HUANGJIN169/CAE32/Mecanismos/Archivos_STL/Modulo_AS5600_p/1.png

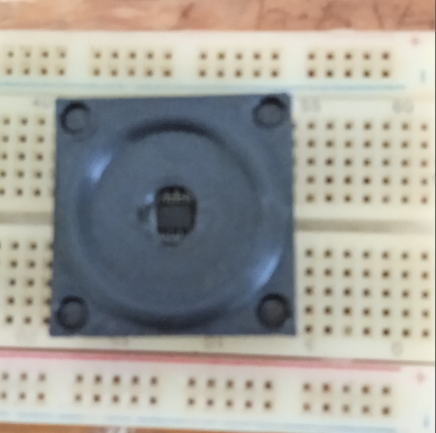
Mecanismos/Archivos_STL/Modulo_AS5600_p/1.png
