HUANGJIN169/CAE32/Mecanismos/Archivos_STL/D#2/EJE_reatroalimentacion-Body.3mf.amf

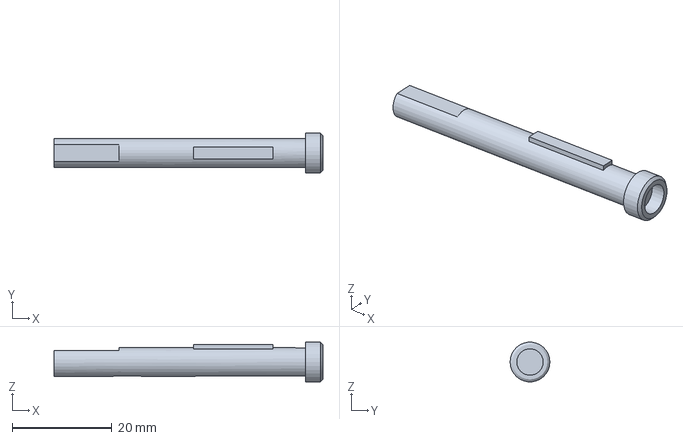
[picture p27: CAD file, 2023-01-21]
Mecanismos/Archivos_STL/D#2/EJE_reatroalimentacion-Body.3mf.amf
54.0 x 8.00 x 7.96 mm
