HUANGJIN169/CAE32/Mecanismos/Archivos_STL/Modulo_AS5600_p/Struct_1.stl

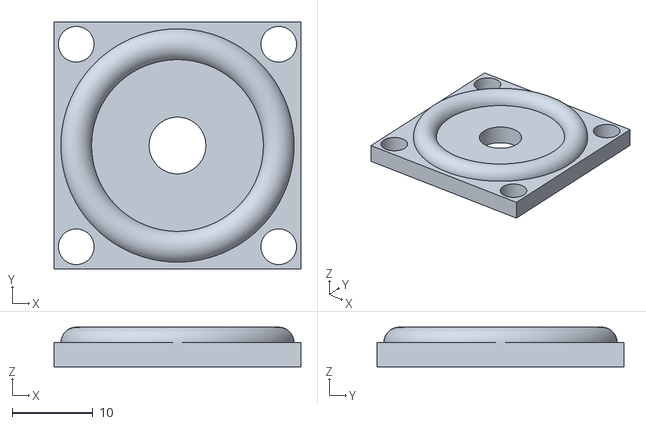
[picture p28: CAD file, 2022-06-30]
Mecanismos/Archivos_STL/Modulo_AS5600_p/Struct_1.stl
30.5 x 30.5 x 4.90
