HUANGJIN169/CAE32/Mecanismos/Shifter/amf/soporte-Body.amf

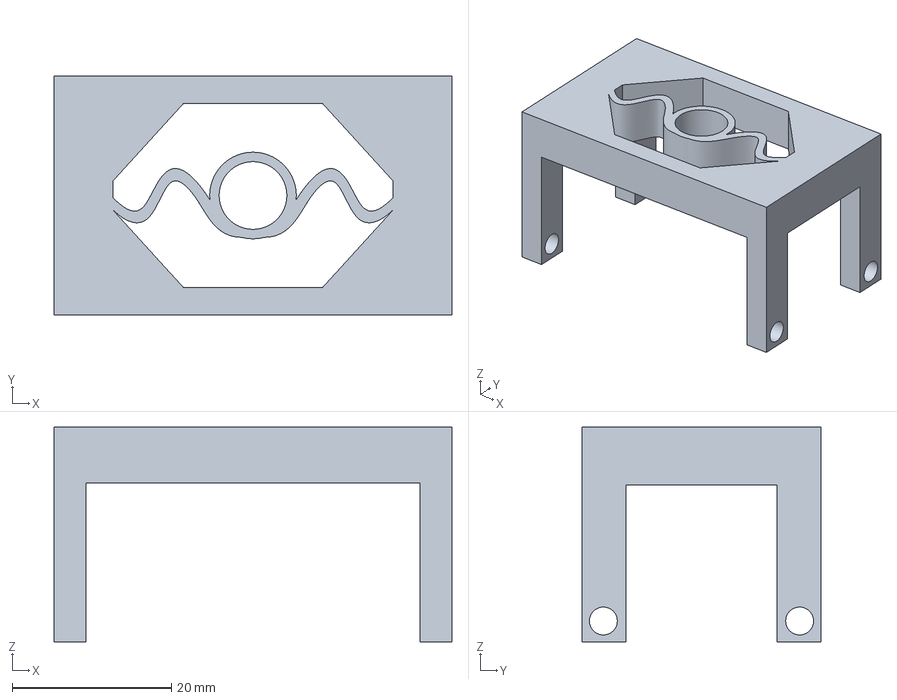
[picture p29: CAD file, 2023-01-31]
Mecanismos/Shifter/amf/soporte-Body.amf
50.0 x 30.0 x 27.0 mm
