HUANGJIN169/CAE32/Mecanismos/Shifter/Tapa.FCStd

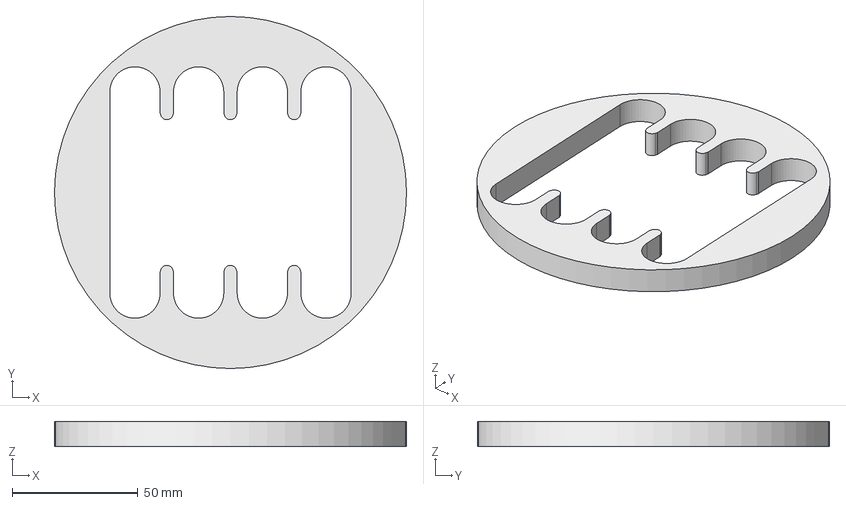
[picture p30: CAD file, 2023-01-31]
Mecanismos/Shifter/Tapa.FCStd
140.0 x 140.0 x 10.0 mm
