HUANGJIN169/CAE32/Mecanismos/Archivos_freecad/Banco_de_pruebas_AS5600/Ensamble_modulo_as5600/Base_iman_bal.FCStd

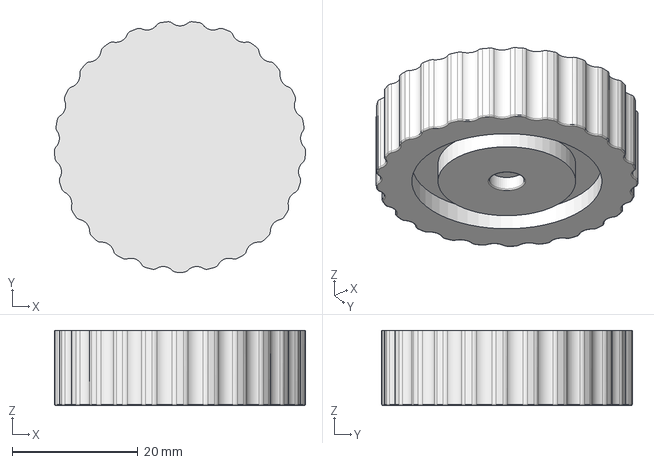
[picture p31: CAD file, 2022-06-30]
Mecanismos/Archivos_freecad/Banco_de_pruebas_AS5600/Ensamble_modulo_as5600/Base_iman_bal.FCStd
40.0 x 39.9 x 12.0 mm
