HUANGJIN169/CAE32/Mecanismos/Archivos_freecad/Case_para_pilas/portapilas.FCStd

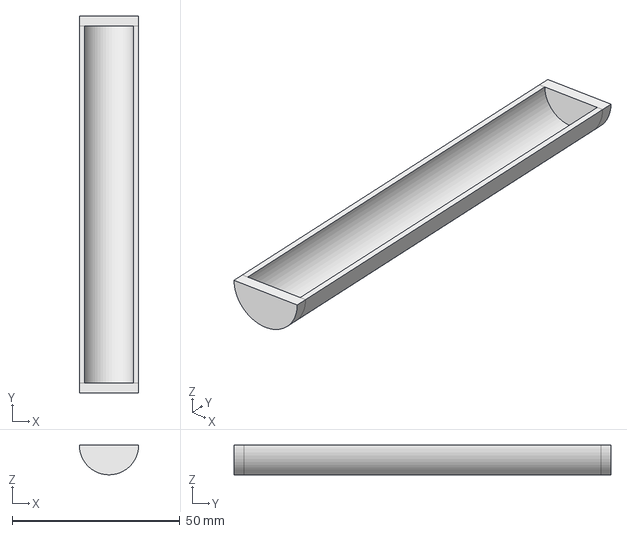
[picture p32: CAD file, 2022-09-12]
Mecanismos/Archivos_freecad/Case_para_pilas/portapilas.FCStd
17.7 x 112.5 x 8.85 mm
