HUANGJIN169/CAE32/Mecanismos/Archivos_freecad/D#2/espaciador.FCStd

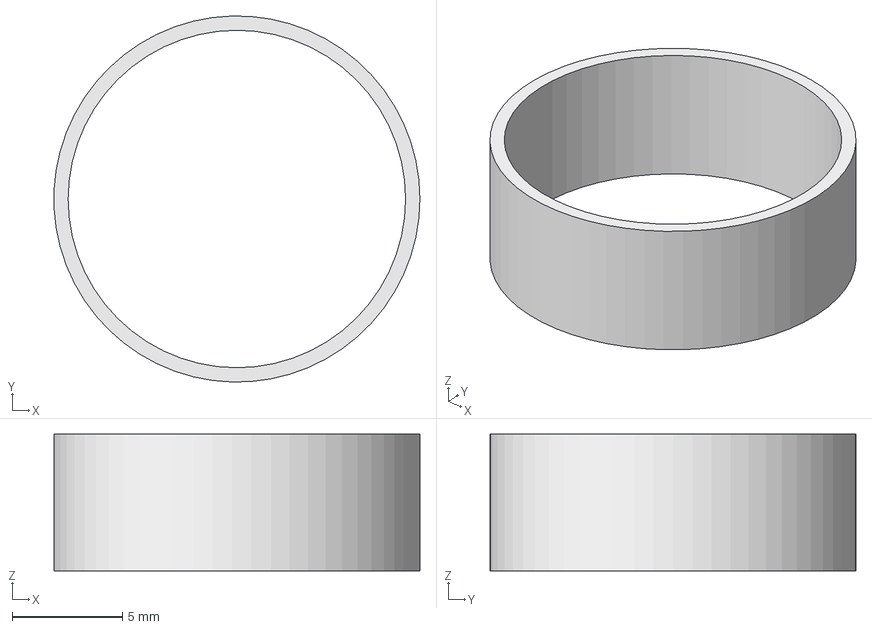
[picture p33: CAD file, 2023-01-21]
Mecanismos/Archivos_freecad/D#2/espaciador.FCStd
16.6 x 16.6 x 6.20 mm
