HUANGJIN169/CAE32/Mecanismos/Archivos_freecad/Simulación_de_pedales/Modelo_1/stl/medidor-Body.stl

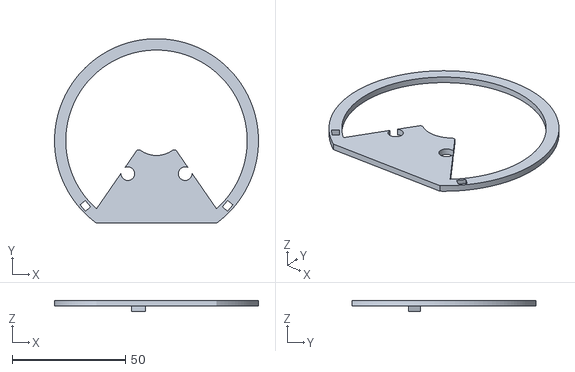
[picture p34: CAD file, 2022-09-18]
Mecanismos/Archivos_freecad/Simulación_de_pedales/Modelo_1/stl/medidor-Body.stl
90.0 x 81.4 x 5.00
