HUANGJIN169/CAE32/Mecanismos/Archivos_freecad/Simulación_de_pedales/Modelo_2/engrane.FCStd

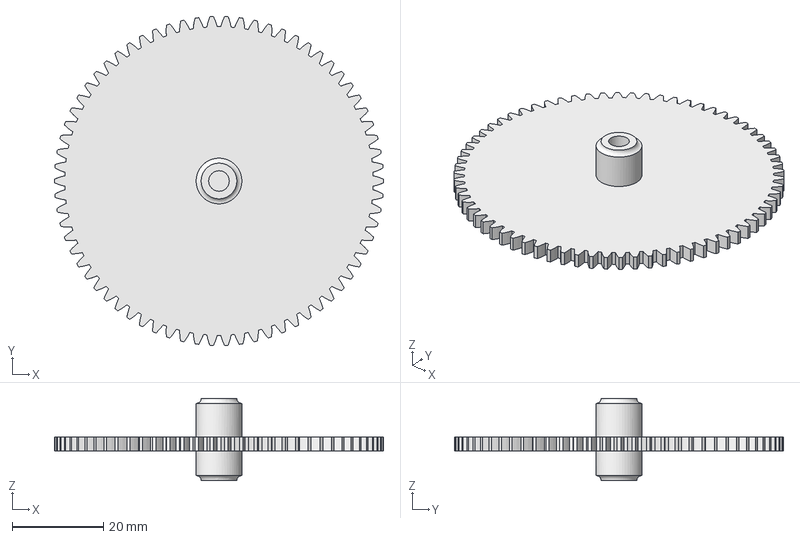
[picture p35: CAD file, 2022-09-12]
Mecanismos/Archivos_freecad/Simulación_de_pedales/Modelo_2/engrane.FCStd
72.0 x 72.0 x 18.0 mm
