HUANGJIN169/CAE32/Mecanismos/Archivos_freecad/Simulación_de_pedales/Modelo_3/Engrane_motor_V2.FCStd

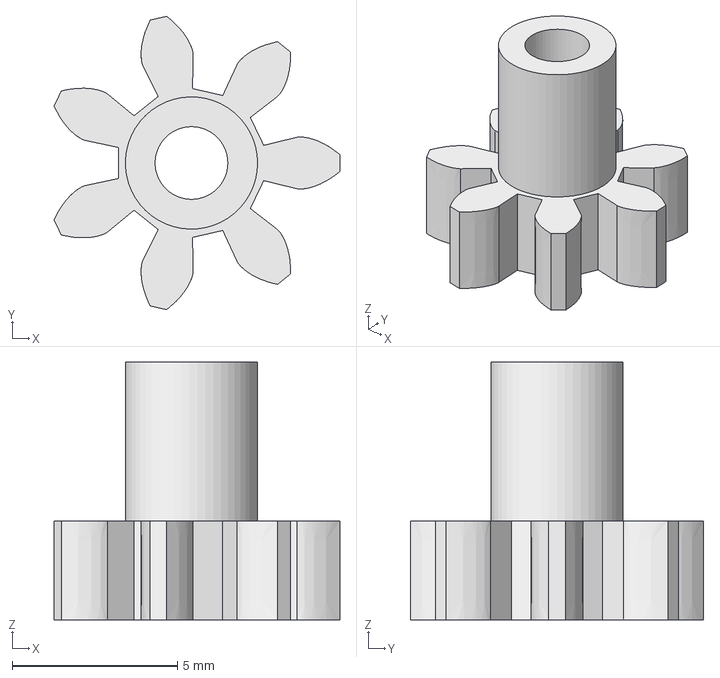
[picture p36: CAD file, 2022-09-15]
Mecanismos/Archivos_freecad/Simulación_de_pedales/Modelo_3/Engrane_motor_V2.FCStd
8.65 x 8.87 x 7.80 mm
