HUANGJIN169/CAE32/Mecanismos/Archivos_freecad/Simulación_de_pedales/Modelo_4/display.FCStd

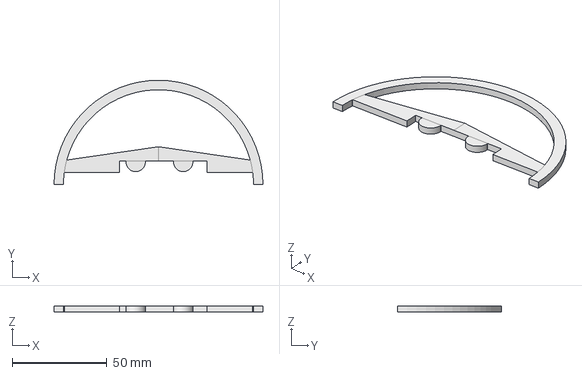
[picture p37: CAD file, 2022-09-12]
Mecanismos/Archivos_freecad/Simulación_de_pedales/Modelo_4/display.FCStd
110.0 x 55.0 x 3.00 mm
