HUANGJIN169/CAE32/Mecanismos/Archivos_freecad/Sistema_mecanico_pedales/Pedales/freno_embrague.FCStd

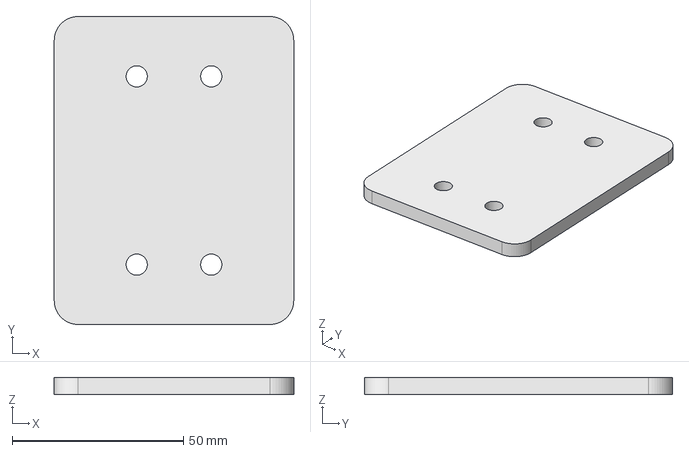
[picture p38: CAD file, 2022-07-07]
Mecanismos/Archivos_freecad/Sistema_mecanico_pedales/Pedales/freno_embrague.FCStd
70.0 x 90.0 x 5.00 mm
