HUANGJIN169/CAE32/Mecanismos/Archivos_freecad/Banco_de_pruebas_AS5600/Ensamble_modulo_as5600/Modulo_as5600.FCStd

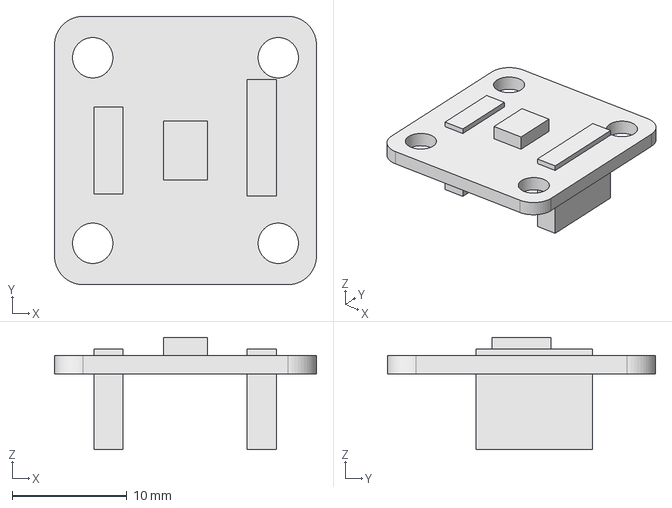
[picture p39: CAD file, 2022-06-30]
Mecanismos/Archivos_freecad/Banco_de_pruebas_AS5600/Ensamble_modulo_as5600/Modulo_as5600.FCStd
22.9 x 23.4 x 9.80 mm
