HUANGJIN169/CAE32/Mecanismos/Archivos_freecad/Simulación_de_pedales/Modelo_1/stl/tope2-Body.stl

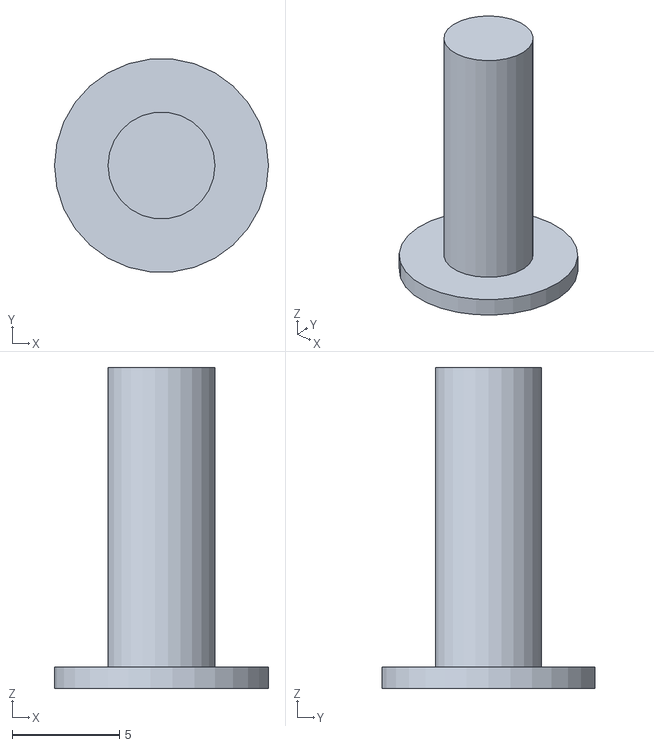
[picture p40: CAD file, 2022-09-18]
Mecanismos/Archivos_freecad/Simulación_de_pedales/Modelo_1/stl/tope2-Body.stl
10.0 x 9.95 x 15.0
