HUANGJIN169/CAE32/Mecanismos/Archivos_freecad/Simulación_de_pedales/Modelo_2/frame.FCStd

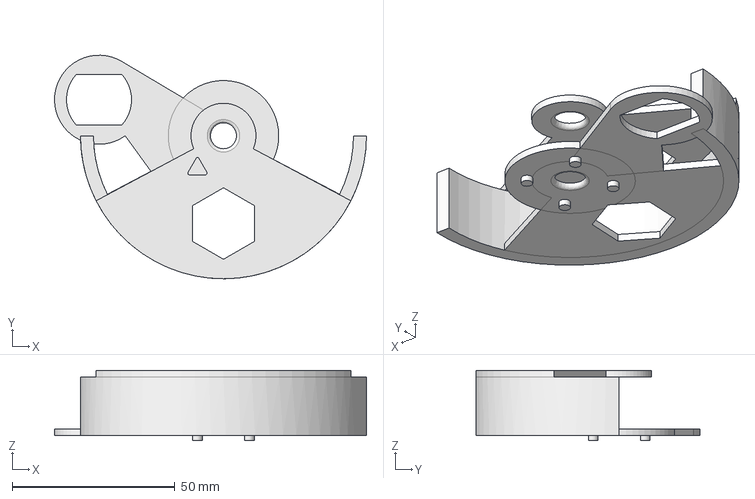
[picture p41: CAD file, 2022-09-12]
Mecanismos/Archivos_freecad/Simulación_de_pedales/Modelo_2/frame.FCStd
96.0 x 68.8 x 21.6 mm
