HUANGJIN169/CAE32/Mecanismos/Archivos_freecad/Simulación_de_pedales/Modelo_3/soporte_marcador2.FCStd

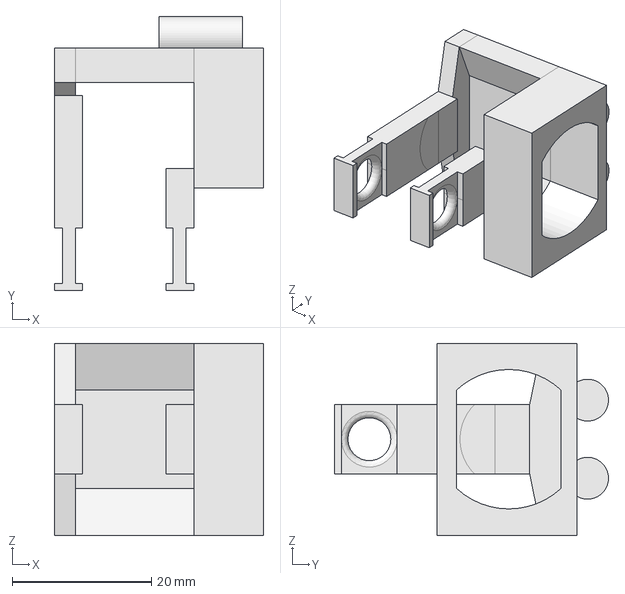
[picture p42: CAD file, 2022-09-12]
Mecanismos/Archivos_freecad/Simulación_de_pedales/Modelo_3/soporte_marcador2.FCStd
30.0 x 39.3 x 27.6 mm
