HUANGJIN169/CAE32/Mecanismos/Archivos_freecad/Simulación_de_pedales/Modelo_4/soporteuno.FCStd

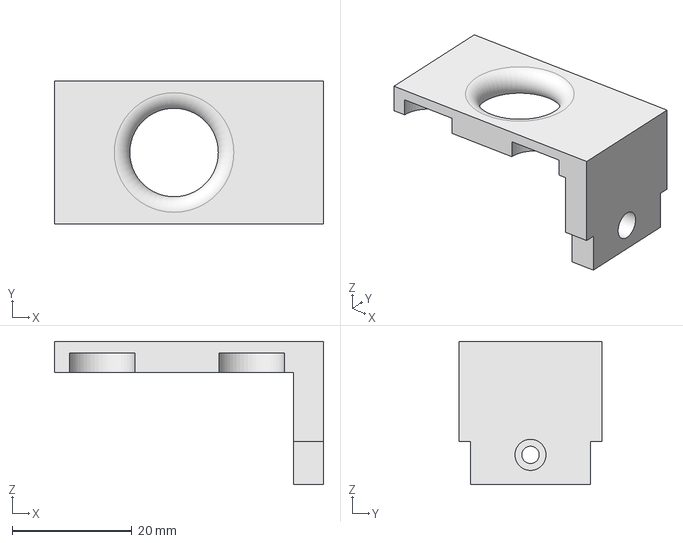
[picture p43: CAD file, 2022-09-12]
Mecanismos/Archivos_freecad/Simulación_de_pedales/Modelo_4/soporteuno.FCStd
45.0 x 24.0 x 24.0 mm
