HUANGJIN169/CAE32/Mecanismos/Archivos_freecad/Simulación_de_pedales/Piezas_frecuentes/medidor.FCStd

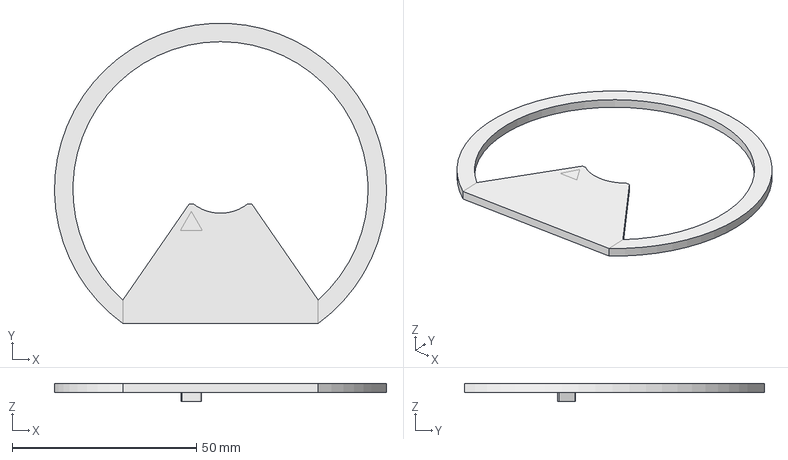
[picture p44: CAD file, 2022-09-12]
Mecanismos/Archivos_freecad/Simulación_de_pedales/Piezas_frecuentes/medidor.FCStd
90.0 x 81.3 x 5.00 mm
