HUANGJIN169/CAE32/Mecanismos/Archivos_STL/D#2/Eje_engrane.amf

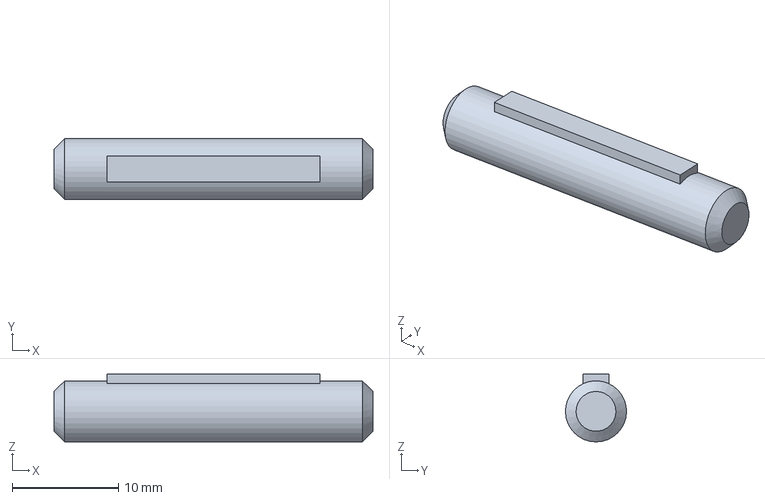
[picture p45: CAD file, 2023-01-21]
Mecanismos/Archivos_STL/D#2/Eje_engrane.amf
30.0 x 5.75 x 6.39 mm
