HUANGJIN169/CAE32/Mecanismos/Archivos_freecad/Simulación_de_pedales/Modelo_3/marcador.FCStd

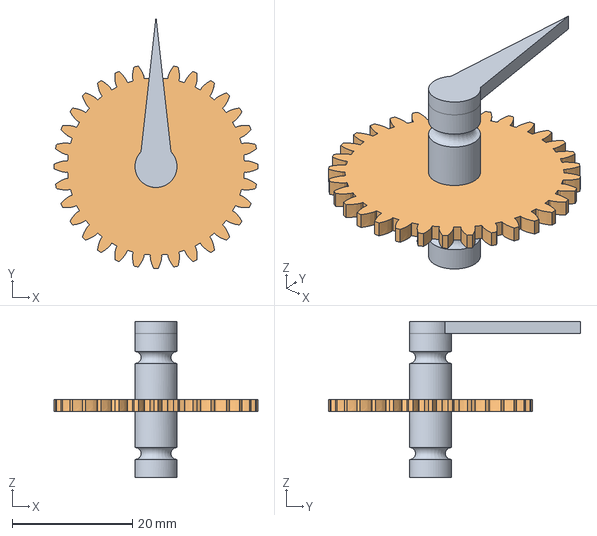
[picture p46: CAD file, 2022-09-12]
Mecanismos/Archivos_freecad/Simulación_de_pedales/Modelo_3/marcador.FCStd
34.0 x 42.0 x 26.0 mm
