HUANGJIN169/CAE32/Mecanismos/Archivos_freecad/Simulación_de_pedales/Modelo_4/Copia de soportedos.FCStd

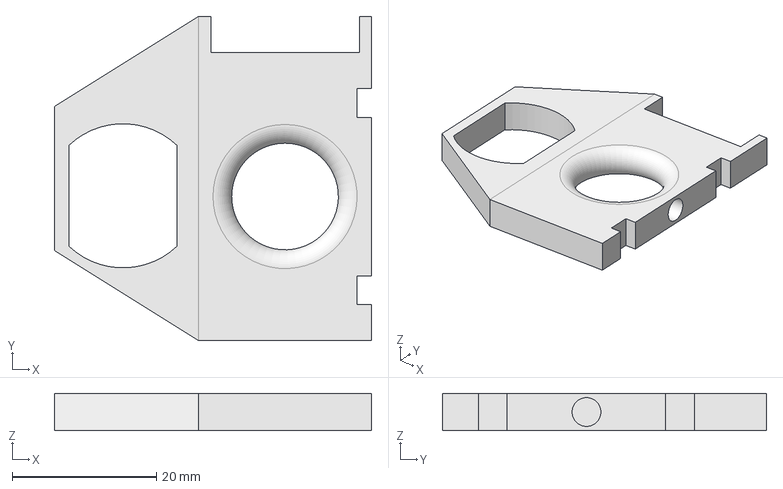
[picture p47: CAD file, 2022-09-12]
Mecanismos/Archivos_freecad/Simulación_de_pedales/Modelo_4/Copia de soportedos.FCStd
44.0 x 45.0 x 5.20 mm
