HUANGJIN169/CAE32/Mecanismos/Archivos_freecad/Simulación_de_pedales/Piezas_frecuentes/motores.FCStd

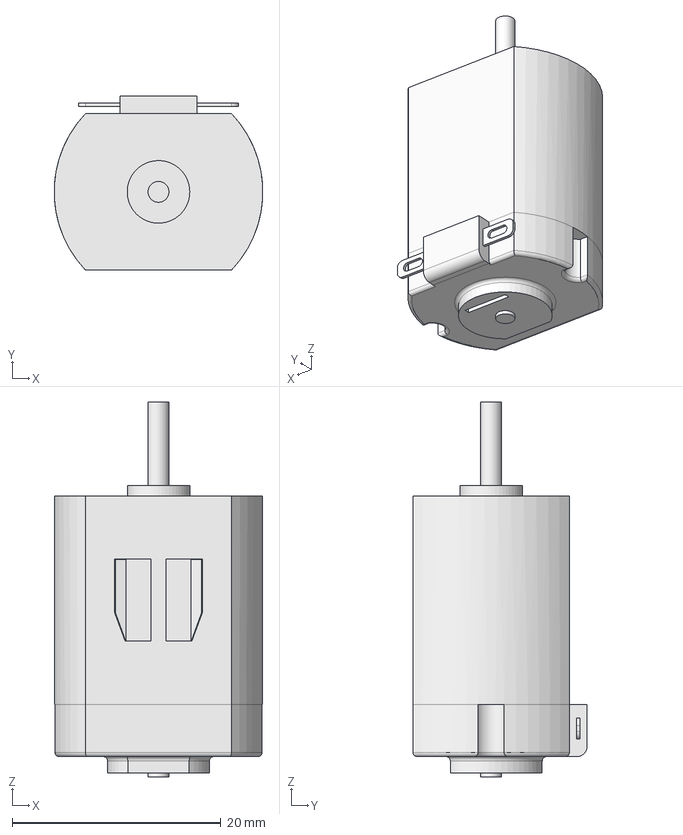
[picture p48: CAD file, 2022-09-12]
Mecanismos/Archivos_freecad/Simulación_de_pedales/Piezas_frecuentes/motores.FCStd
20.0 x 16.7 x 36.0 mm
