HUANGJIN169/CAE32/Mecanismos/Archivos_STL/D#2/Engrane_Parametrico-BodyPocket.amf

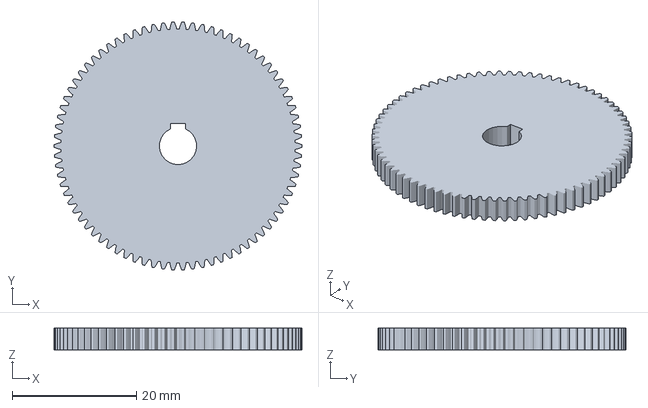
[picture p49: CAD file, 2023-01-21]
Mecanismos/Archivos_STL/D#2/Engrane_Parametrico-BodyPocket.amf
40.0 x 40.0 x 3.50 mm
