HUANGJIN169/CAE32/Mecanismos/Archivos_freecad/Banco_de_pruebas_AS5600/Ensamble_modulo_as5600/iman.FCStd

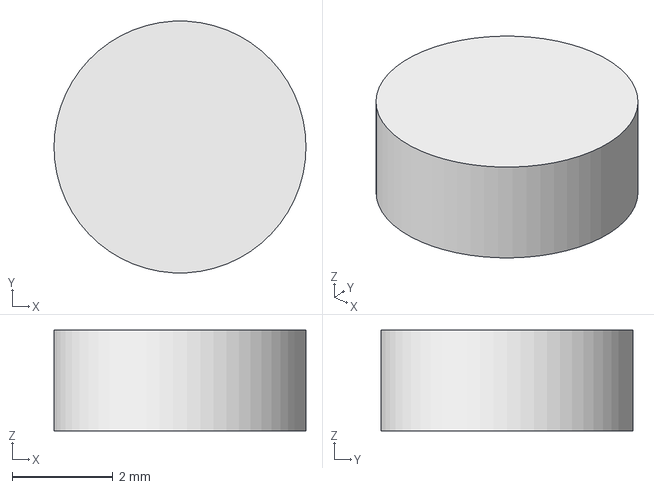
[picture p50: CAD file, 2022-06-30]
Mecanismos/Archivos_freecad/Banco_de_pruebas_AS5600/Ensamble_modulo_as5600/iman.FCStd
5.00 x 4.99 x 2.00 mm
