HUANGJIN169/CAE32/Mecanismos/Archivos_freecad/D#2/case1.FCStd

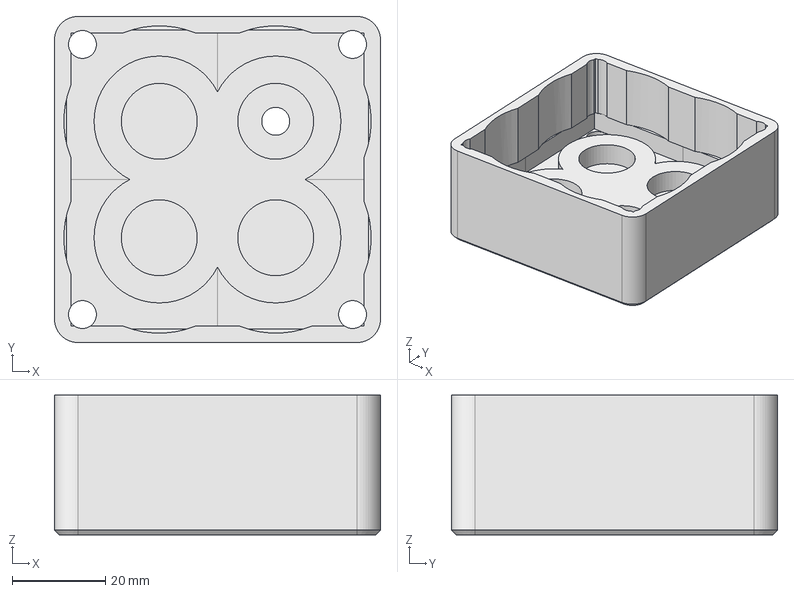
[picture p51: CAD file, 2022-11-13]
Mecanismos/Archivos_freecad/D#2/case1.FCStd
70.0 x 70.0 x 30.0 mm
