HUANGJIN169/CAE32/Mecanismos/Archivos_freecad/Simulación_de_pedales/Modelo_1/imprimir.FCStd

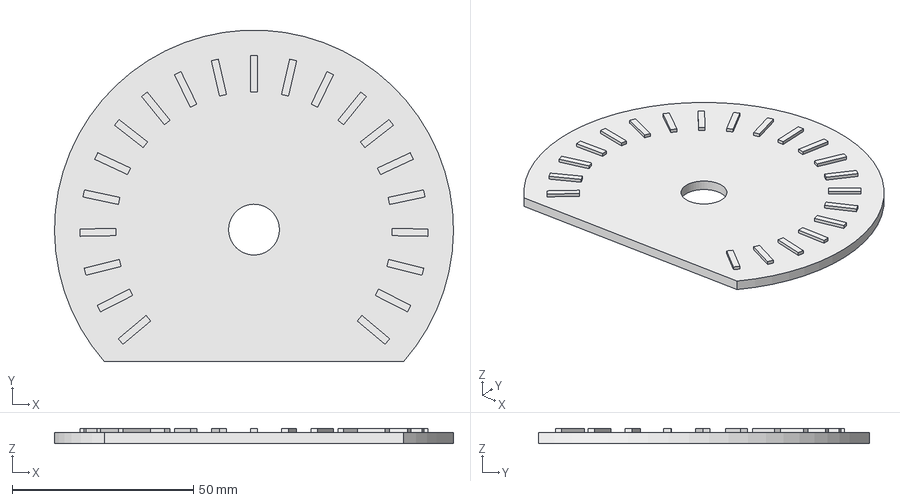
[picture p52: CAD file, 2022-09-18]
Mecanismos/Archivos_freecad/Simulación_de_pedales/Modelo_1/imprimir.FCStd
110.0 x 91.3 x 4.00 mm
