HUANGJIN169/CAE32/Mecanismos/Archivos_freecad/Simulación_de_pedales/Modelo_1/stl/intermedio-Body.stl

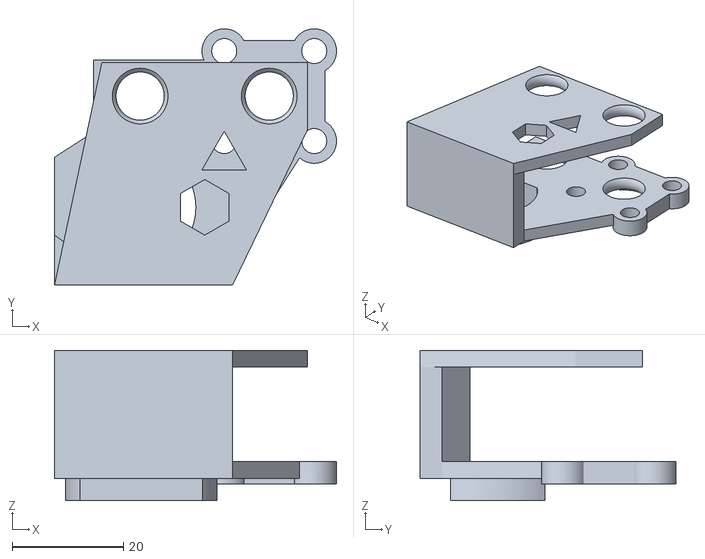
[picture p53: CAD file, 2022-09-16]
Mecanismos/Archivos_freecad/Simulación_de_pedales/Modelo_1/stl/intermedio-Body.stl
50.7 x 46.1 x 27.0
