HUANGJIN169/CAE32/Mecanismos/Archivos_freecad/Simulación_de_pedales/Modelo_4/union_apuntador.FCStd

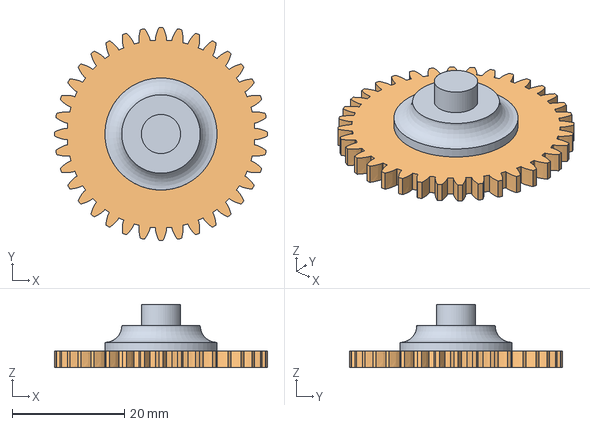
[picture p54: CAD file, 2022-09-12]
Mecanismos/Archivos_freecad/Simulación_de_pedales/Modelo_4/union_apuntador.FCStd
38.0 x 38.0 x 11.3 mm
