HUANGJIN169/CAE32/Mecanismos/Archivos_freecad/D#2/Balero_Parametrico.FCStd

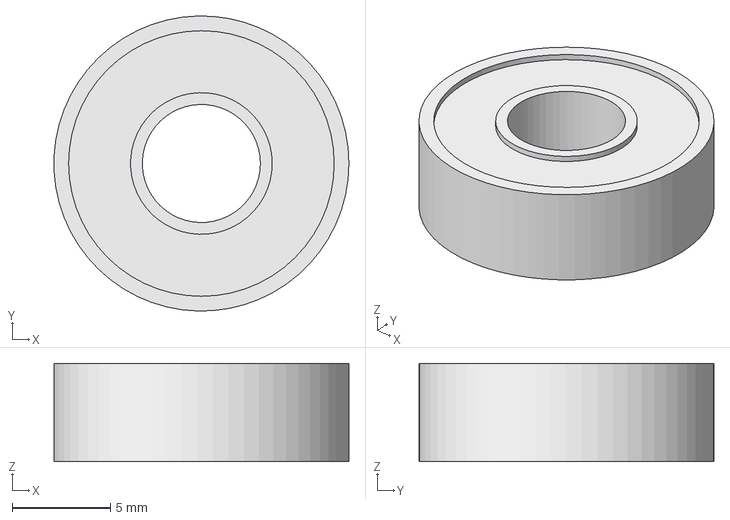
[picture p55: CAD file, 2022-11-08]
Mecanismos/Archivos_freecad/D#2/Balero_Parametrico.FCStd
15.0 x 15.0 x 5.00 mm
