HUANGJIN169/CAE32/Mecanismos/Archivos_freecad/Simulación_de_pedales/Modelo_1/stl/EngraneApuntador-Fusion.stl

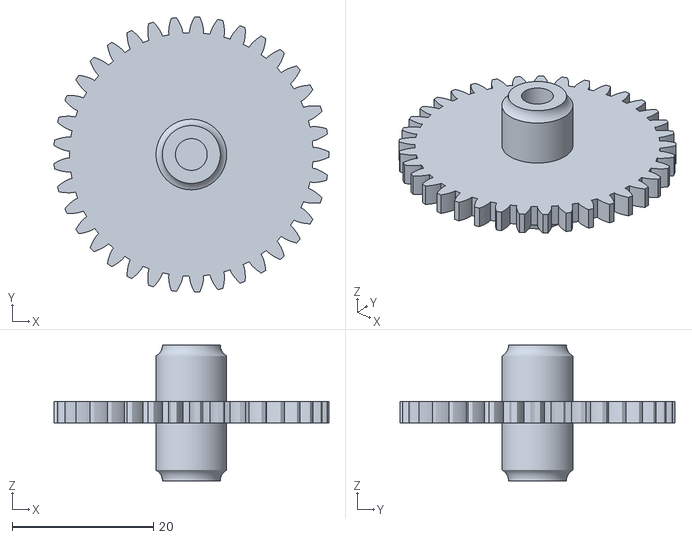
[picture p56: CAD file, 2022-09-16]
Mecanismos/Archivos_freecad/Simulación_de_pedales/Modelo_1/stl/EngraneApuntador-Fusion.stl
39.0 x 39.0 x 19.2
