HUANGJIN169/CAE32/Mecanismos/Archivos_freecad/Simulación_de_pedales/Modelo_1/tope2.FCStd

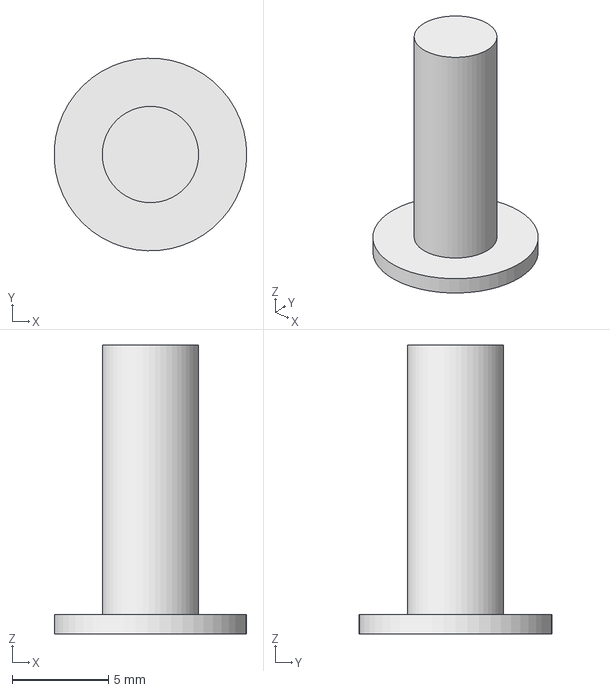
[picture p57: CAD file, 2022-09-18]
Mecanismos/Archivos_freecad/Simulación_de_pedales/Modelo_1/tope2.FCStd
9.99 x 10.00 x 15.0 mm
