HUANGJIN169/CAE32/Mecanismos/Archivos_freecad/Simulación_de_pedales/Modelo_4/engrane_motor.FCStd

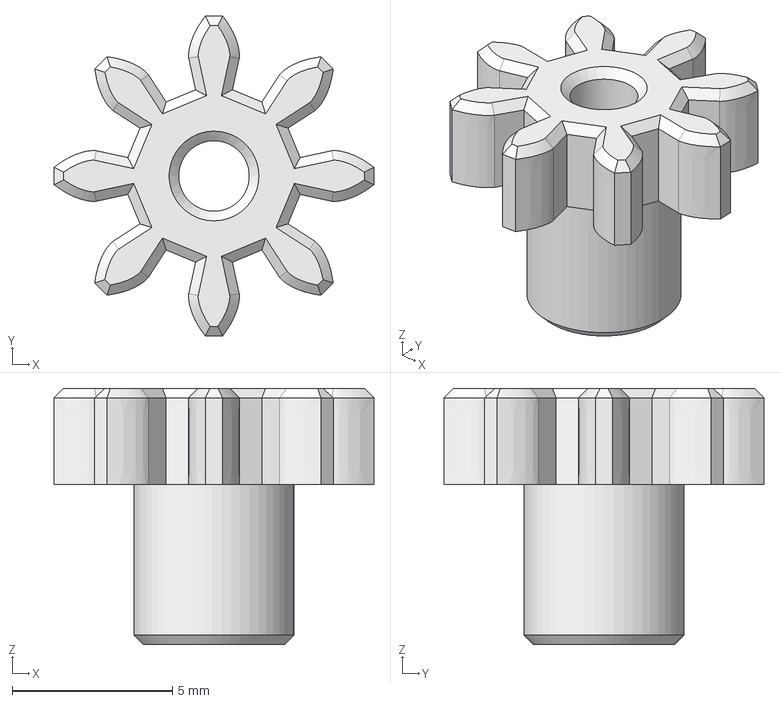
[picture p58: CAD file, 2022-09-12]
Mecanismos/Archivos_freecad/Simulación_de_pedales/Modelo_4/engrane_motor.FCStd
9.99 x 9.99 x 8.00 mm
