HUANGJIN169/CAE32/Mecanismos/Archivos_freecad/D#2/Engrane_D15.FCStd

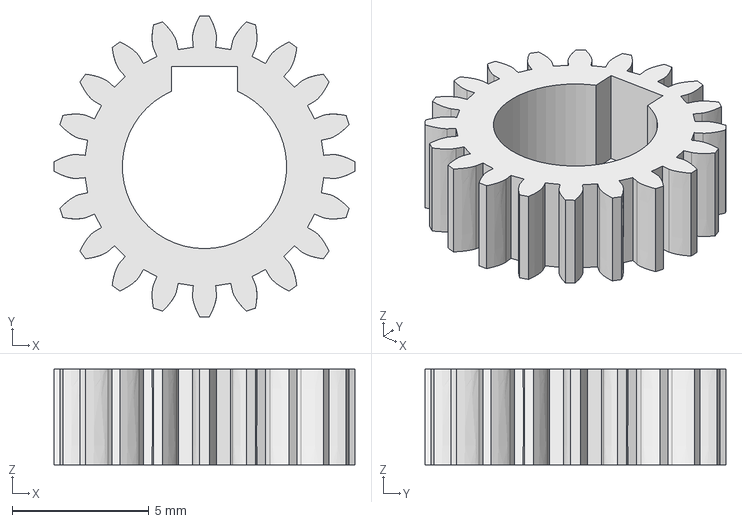
[picture p59: CAD file, 2022-11-08]
Mecanismos/Archivos_freecad/D#2/Engrane_D15.FCStd
11.0 x 11.0 x 3.50 mm
