HUANGJIN169/CAE32/Mecanismos/Archivos_freecad/Simulación_de_pedales/Modelo_1/stl/engraneMotriz-Body.stl

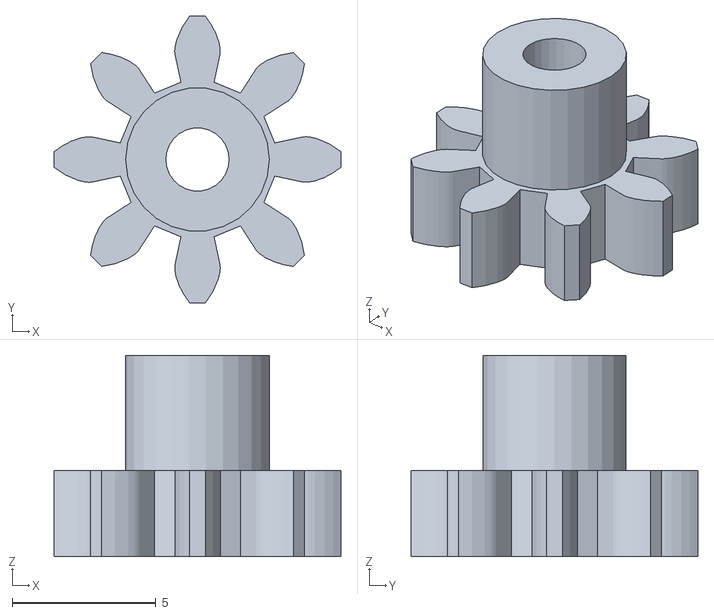
[picture p60: CAD file, 2022-09-16]
Mecanismos/Archivos_freecad/Simulación_de_pedales/Modelo_1/stl/engraneMotriz-Body.stl
9.99 x 9.99 x 7.00
