HUANGJIN169/CAE32/Mecanismos/Archivos_freecad/Simulación_de_pedales/Modelo_1/union.FCStd

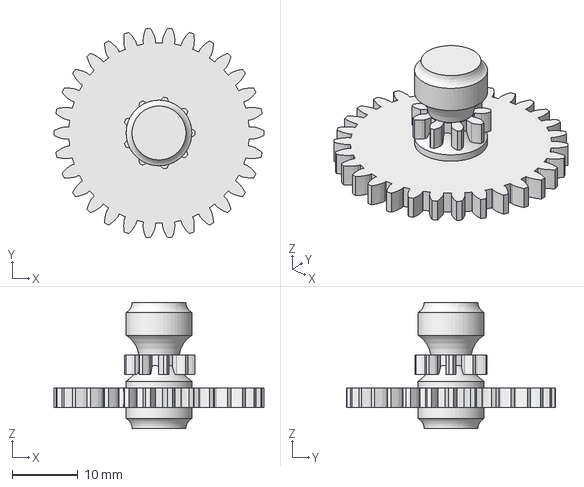
[picture p61: CAD file, 2022-09-16]
Mecanismos/Archivos_freecad/Simulación_de_pedales/Modelo_1/union.FCStd
32.0 x 31.9 x 19.2 mm
