HUANGJIN169/CAE32/Mecanismos/Archivos_freecad/Simulación_de_pedales/Modelo_4/porta_iman.FCStd

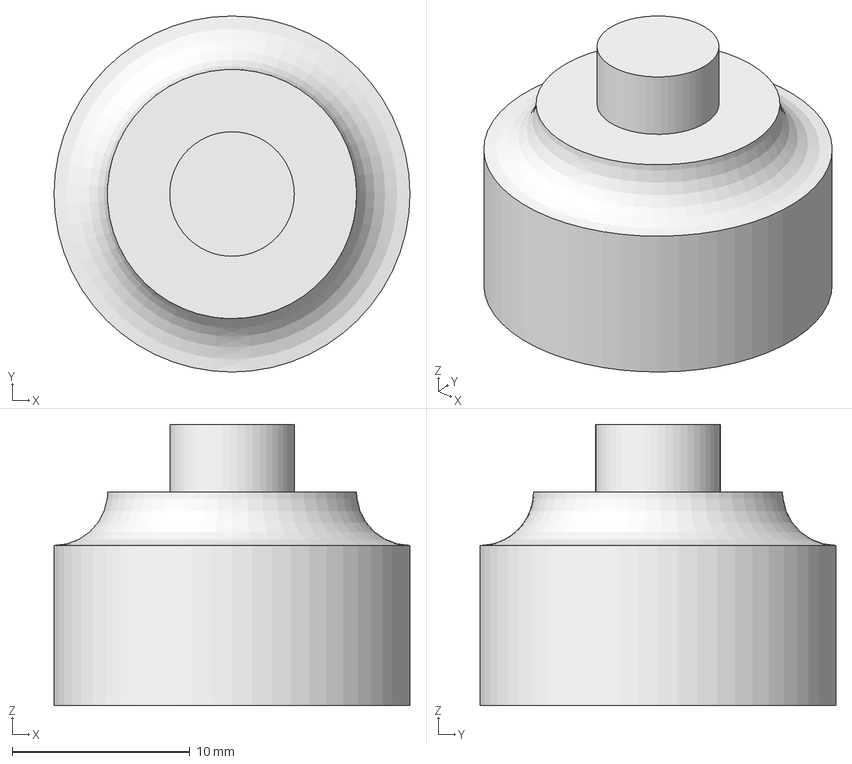
[picture p63: CAD file, 2022-09-12]
Mecanismos/Archivos_freecad/Simulación_de_pedales/Modelo_4/porta_iman.FCStd
20.0 x 20.0 x 15.8 mm
