HUANGJIN169/CAE32/Mecanismos/Archivos_freecad/D#2/case1-Body.3mf

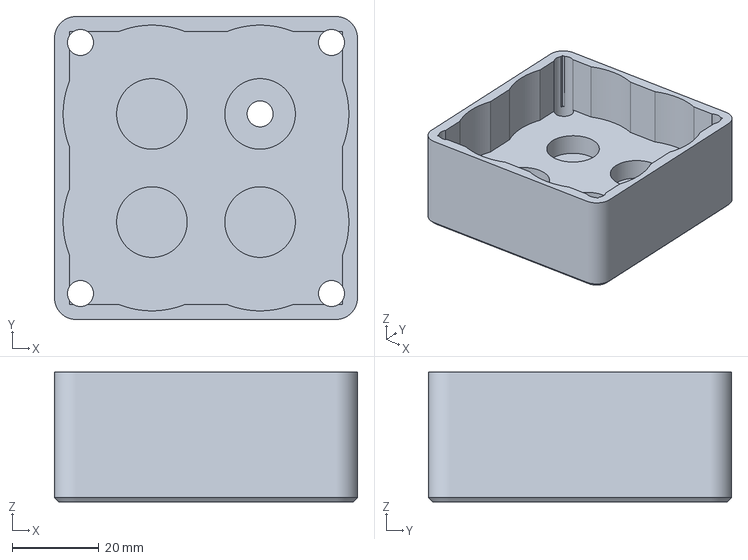
[picture p64: CAD file, 2022-11-08]
Mecanismos/Archivos_freecad/D#2/case1-Body.3mf
70.0 x 70.0 x 30.0 mm
