HUANGJIN169/CAE32/Mecanismos/Archivos_freecad/Simulación_de_pedales/Modelo_1/stl/Superior-Body.stl

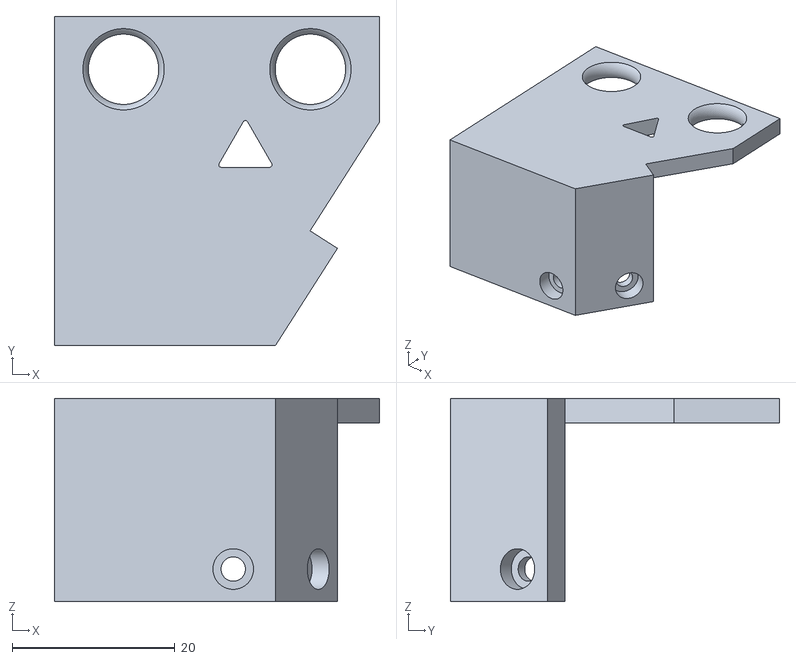
[picture p65: CAD file, 2022-09-12]
Mecanismos/Archivos_freecad/Simulación_de_pedales/Modelo_1/stl/Superior-Body.stl
40.0 x 40.5 x 25.0
