HUANGJIN169/CAE32/Mecanismos/Archivos_freecad/Simulación_de_pedales/Modelo_4/soporte_genereal.FCStd

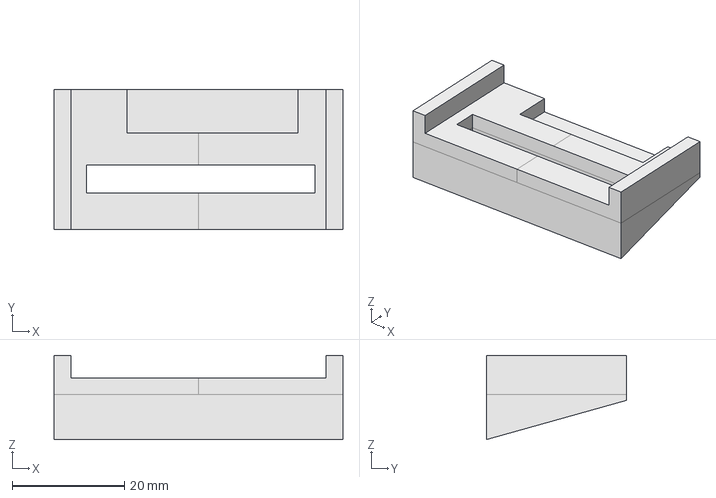
[picture p66: CAD file, 2022-09-12]
Mecanismos/Archivos_freecad/Simulación_de_pedales/Modelo_4/soporte_genereal.FCStd
51.5 x 25.0 x 15.0 mm
