HUANGJIN169/CAE32/Mecanismos/Archivos_freecad/Simulación_de_pedales/Modelo_4/soporte_iman.FCStd

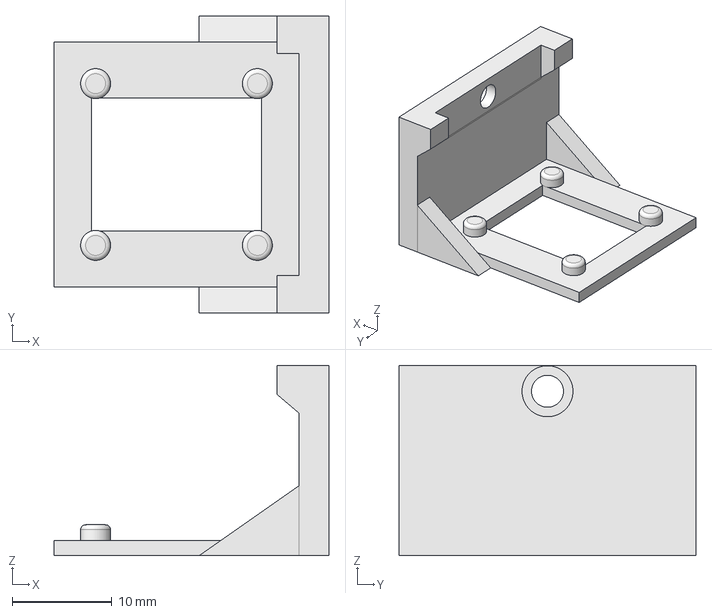
[picture p67: CAD file, 2022-09-12]
Mecanismos/Archivos_freecad/Simulación_de_pedales/Modelo_4/soporte_iman.FCStd
27.5 x 29.7 x 19.1 mm
