HUANGJIN169/CAE32/Mecanismos/Archivos_freecad/D#2/Engrane_Motor.FCStd

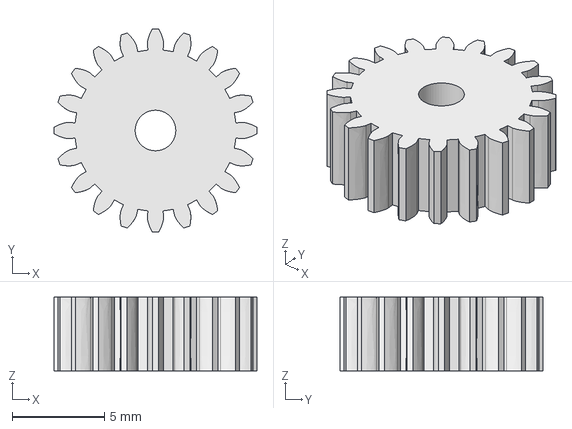
[picture p68: CAD file, 2022-11-08]
Mecanismos/Archivos_freecad/D#2/Engrane_Motor.FCStd
11.0 x 11.0 x 4.00 mm
