HUANGJIN169/CAE32/Mecanismos/Archivos_freecad/Simulación_de_pedales/Modelo_4/apuntador.FCStd

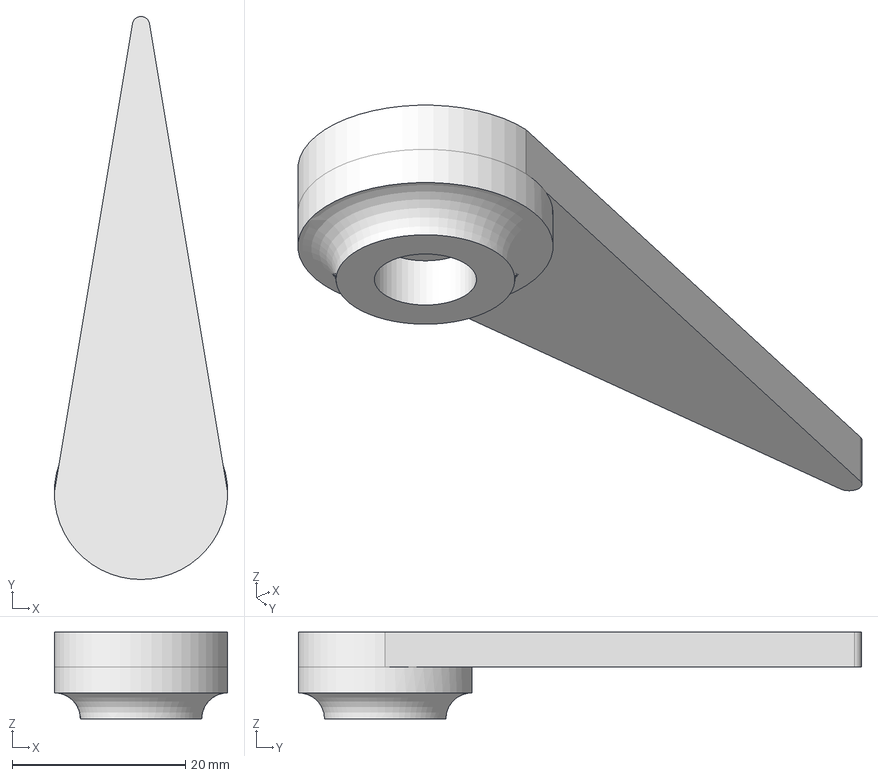
[picture p69: CAD file, 2022-09-12]
Mecanismos/Archivos_freecad/Simulación_de_pedales/Modelo_4/apuntador.FCStd
20.0 x 64.9 x 10.0 mm
