HUANGJIN169/CAE32/Mecanismos/Archivos_freecad/D#2/Engrane_D50.FCStd

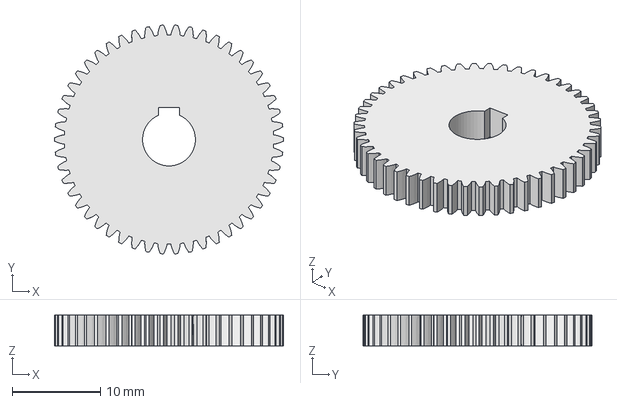
[picture p70: CAD file, 2022-11-08]
Mecanismos/Archivos_freecad/D#2/Engrane_D50.FCStd
26.0 x 26.0 x 3.50 mm
