HUANGJIN169/CAE32/Código_ESP_IDF/components/CAE32/include/ControladorI2c.h

esp_err_t i2c_lectura(uint8_t slave_addr, uint8_t reg_addr, uint8_t *data, uint16_t len);
void i2c_escritura(uint8_t addr,uint8_t reg_addr,uint8_t data);
void RutinaDeConfiguracionManual(void);
void RutinaDeConfiguracionAutomatica();
void ConfiguracionMaxAng();
void LeerRawAngle();
void EscribirTramaDeDatosAEncoder(uint8_t reg_addr0,uint8_t reg_addr1,uint8_t dato0,uint8_t dato1);
void MoverSentidoHorario(float cicloDeTrabajo);
void MoverSentidoAntihorario(float cicloDeTrabajo);
