HUANGJIN169/CAE32/Codigo/Interfaz_grafica/Interfaz_gtk/src/signals.c

/* Signals to handle events
 *
 *
 *
#include "signals.h"
#include <gdk/gdkx.h>
#include <glib.h>
#include <gtk/gtk.h>
void printgtk(ObjectsUI obj) {
  g_printerr("test\n");
  // levelBarValue(obj);
}
*/
