HUANGJIN169/CAE32/Código_ESP_IDF/components/CAE32/src/Pedales.c

Pedal* Acelerador={
    Canal=ADC1_CHANNEL_0;
    ResoluciónBits=8;   //8 bits = 255, 16 bits = 4096
    TPedal="A";          //A de Acelerador, sirve para que sea posible identificarlo
    ValorADCRaw=NULL;
    ValorMapeado=NULL;
    Error=0;
    Giro=0;

};

Pedal Freno={
    
    }
