HUANGJIN169/CAE32/Código_ESP_IDF/components/CAE32/src/ConfADC.c

#include "driver/adc.h" 

#define ADC_ATT 1.750/4095
#define ADC_CHANNEL_ANGULO ADC1_CHANNEL_7
/**
 * Notas
 *  añadir como parametros el canal ADC, resolución a las funciones que lo requieran 
 *  retornar un error si el canal no existe
 * 
 */

/**
 * @brief Inicializa el ADC y específica la resolución del ADC y selecciona el pin de entrada en este caso el pin 35
 * 
 */
void IniciarAdc(){
    adc1_config_width(ADC_WIDTH_BIT_12); 
    adc1_config_channel_atten(ADC_CHANNEL_ANGULO,ADC_ATTEN_DB_6);
}

/**
 * @brief Calcula el voltaje real en base a la atenuación, revise los valores en la API ADC de ESP-IDF
 * 
 * @return float Voltage real
 */
 float calcular_voltaje(){
    return adc1_get_raw(ADC_CHANNEL_ANGULO);
 }

/**
 * @brief Ecuación para obtener los grados Y=0.078*lectura analógica-30.09
 * @return int Grados reales
 */
int VoltajeAGrados(){
    int grados=adc1_get_raw(ADC_CHANNEL_ANGULO)*0.1203-7.5789; 
    return grados;
}
int VoltajeAGradosPtr(int *grados){
    *grados=(int)(adc1_get_raw(ADC_CHANNEL_ANGULO)*0.1203-7.5789); 
    return (*grados>=270||*grados<=0)?1:-1;
}

int ValorADCRaw(int *raw){
    *raw=adc1_get_raw(ADC_CHANNEL_ANGULO);
    return 1;
}

void VoltajeAGradosPtrv(int *grados){
    *grados=(int)(adc1_get_raw(ADC_CHANNEL_ANGULO)*0.1203-7.5789); 
    
    
}
